Machiel80/esp32-serial-flasher/flashbox design/3d model/3d-model impression.png

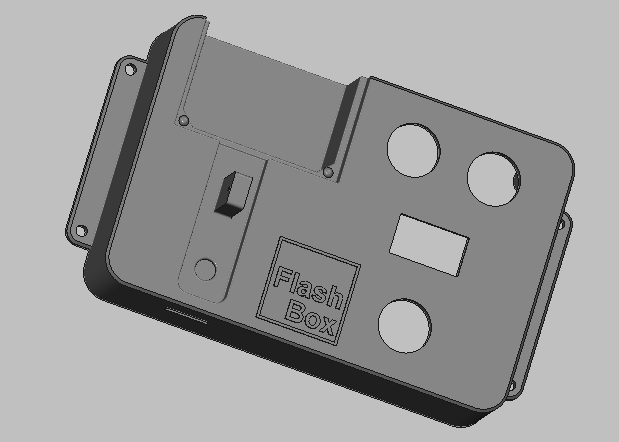
flashbox design/3d model/3d-model impression.png
