Machiel80/esp32-serial-flasher/flashbox design/3d model/20220907_FlashBox_left.png

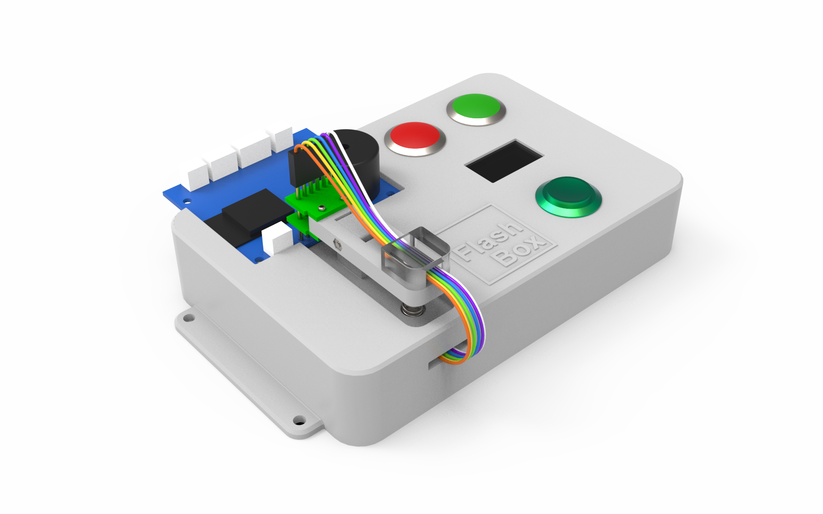
flashbox design/3d model/20220907_FlashBox_left.png
