Machiel80/esp32-serial-flasher/flashbox design/components/1 Usb cable/H7e599deed7ca4eed93aaca98d95c51f6y.jpg

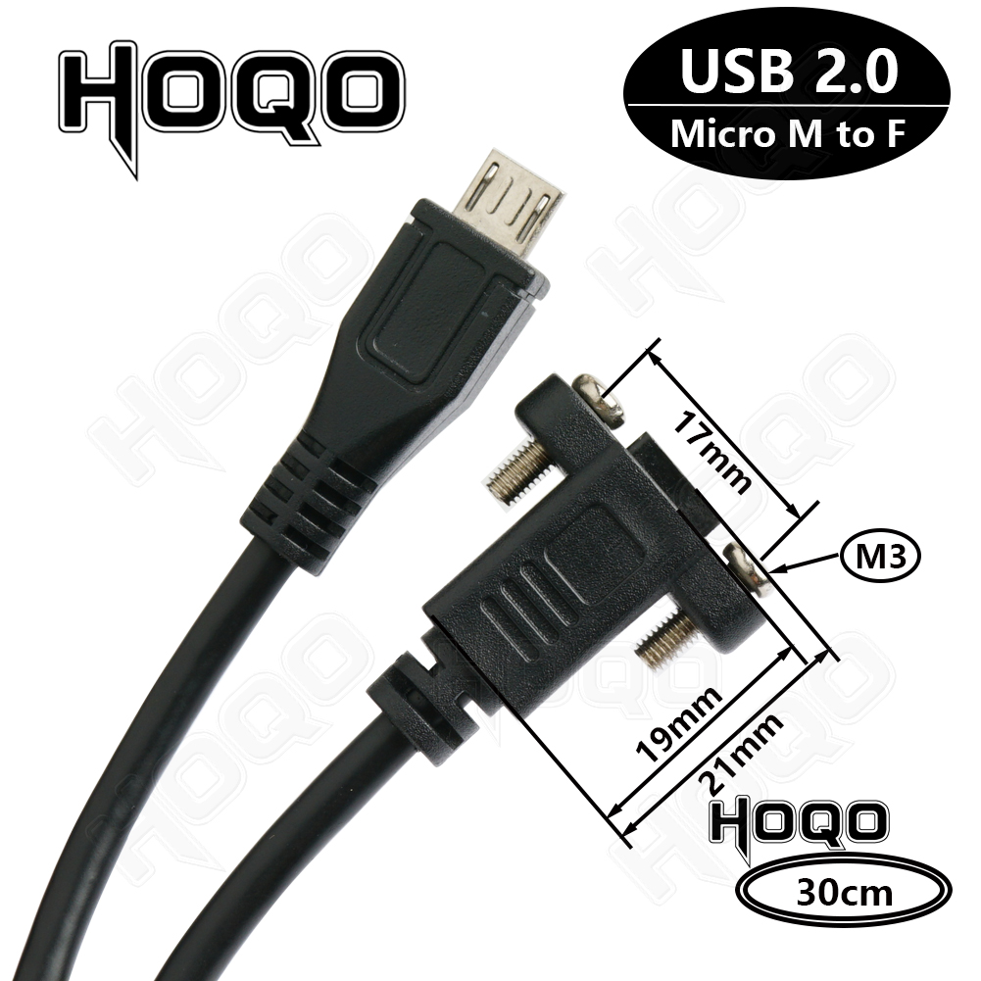
flashbox design/components/1 Usb cable/H7e599deed7ca4eed93aaca98d95c51f6y.jpg
