Machiel80/esp32-serial-flasher/flashbox design/components/1 Usb cable/H70d741a2f5fd48ce99fb8062a469d486L.jpg

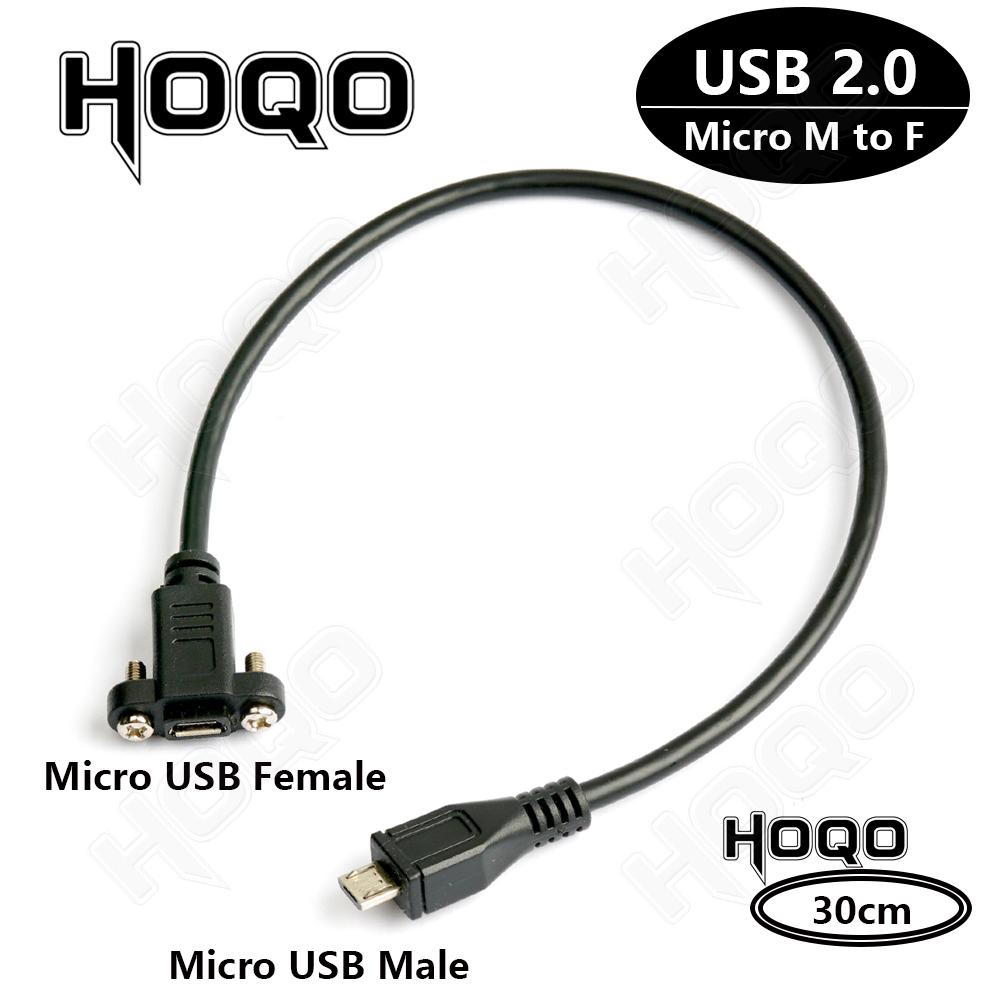
flashbox design/components/1 Usb cable/H70d741a2f5fd48ce99fb8062a469d486L.jpg
