Machiel80/esp32-serial-flasher/flashbox design/components/1 Usb cable/H580205805ddb444d95cb9cb375392fc0s.jpg

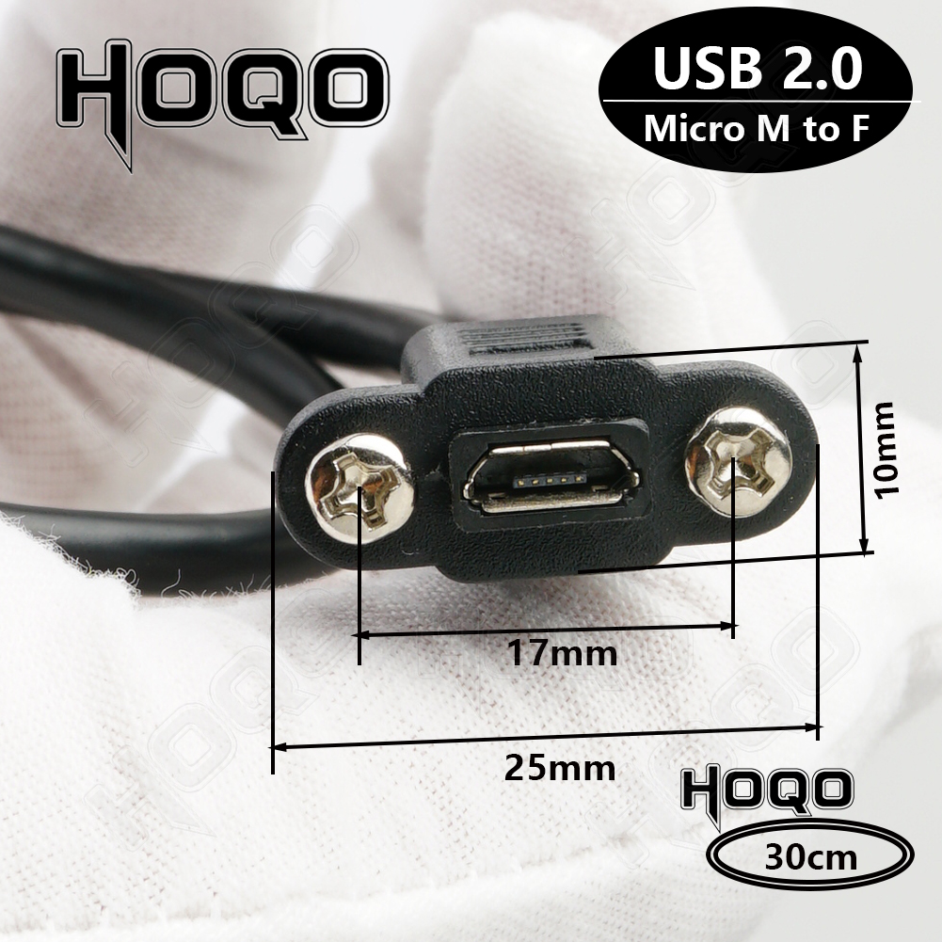
flashbox design/components/1 Usb cable/H580205805ddb444d95cb9cb375392fc0s.jpg
