Machiel80/esp32-serial-flasher/flashbox design/components/2 ESP32 devkit v1/72782579-1bceb700-3c4a-11ea-8157-d8394b984931.png

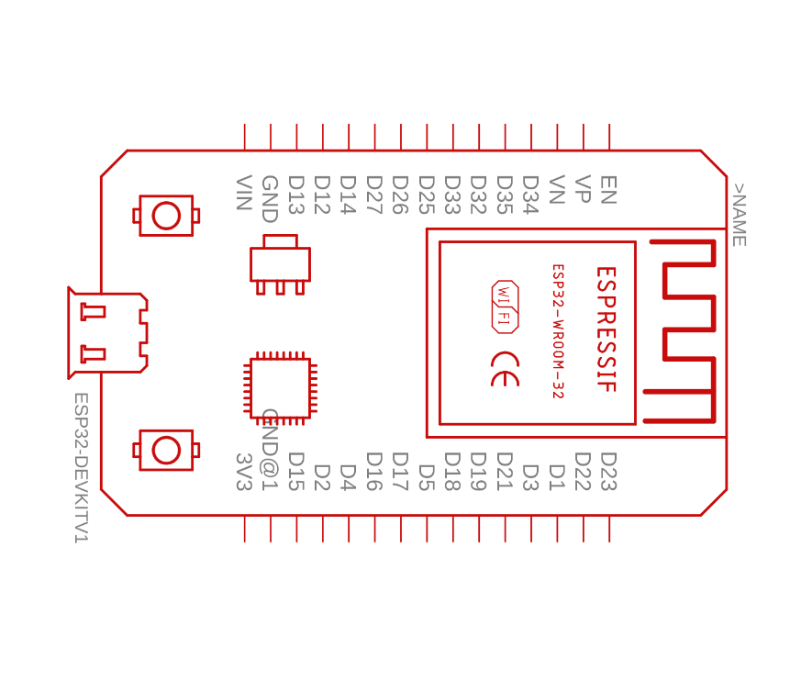
flashbox design/components/2 ESP32 devkit v1/72782579-1bceb700-3c4a-11ea-8157-d8394b984931.png
