Machiel80/esp32-serial-flasher/flashbox design/components/2 ESP32 devkit v1/72782582-1d987a80-3c4a-11ea-8e91-fc3043e2dca8.png

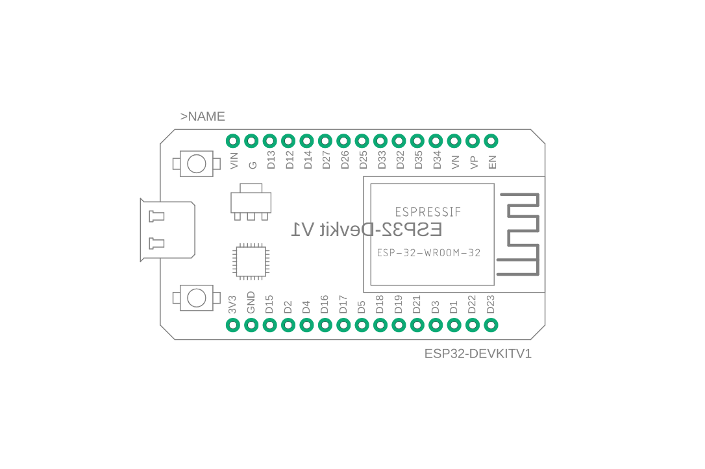
flashbox design/components/2 ESP32 devkit v1/72782582-1d987a80-3c4a-11ea-8e91-fc3043e2dca8.png
