Machiel80/esp32-serial-flasher/flashbox design/components/2 ESP32 devkit v1/edc50841300b4eb69d4db9c68fee543ab487c1be.webp

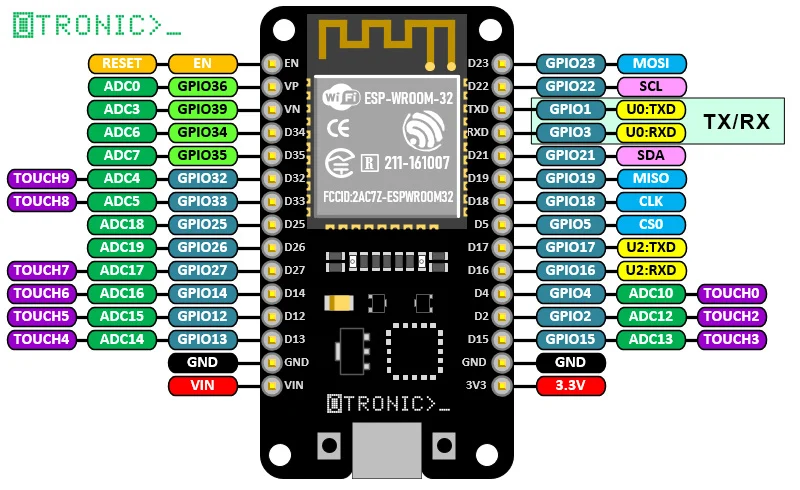
flashbox design/components/2 ESP32 devkit v1/edc50841300b4eb69d4db9c68fee543ab487c1be.webp
