Machiel80/esp32-serial-flasher/flashbox design/components/2 ESP32 devkit v1/HTB1lpVGicrI8KJjy0Fhq6zfnpXa4.webp

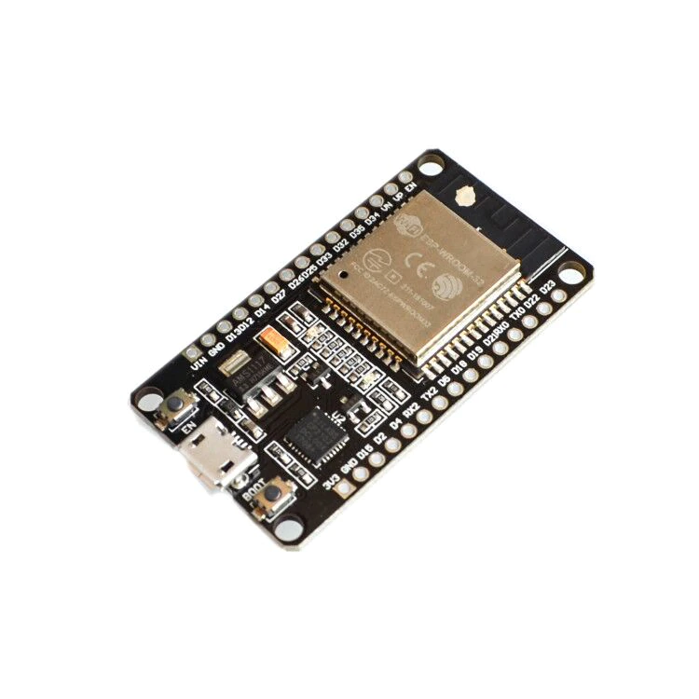
flashbox design/components/2 ESP32 devkit v1/HTB1lpVGicrI8KJjy0Fhq6zfnpXa4.webp
