Machiel80/esp32-serial-flasher/flashbox design/components/2 ESP32 devkit v1/HTB1yfV2if6H8KJjy0Fjq6yXepXax.webp

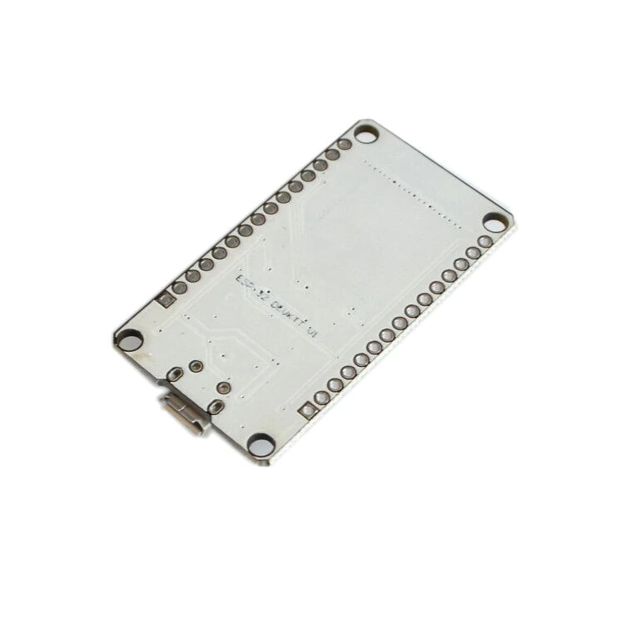
flashbox design/components/2 ESP32 devkit v1/HTB1yfV2if6H8KJjy0Fjq6yXepXax.webp
