Machiel80/esp32-serial-flasher/flashbox design/components/3 Six pin programmer module/41XIdj7KVcL.jpg

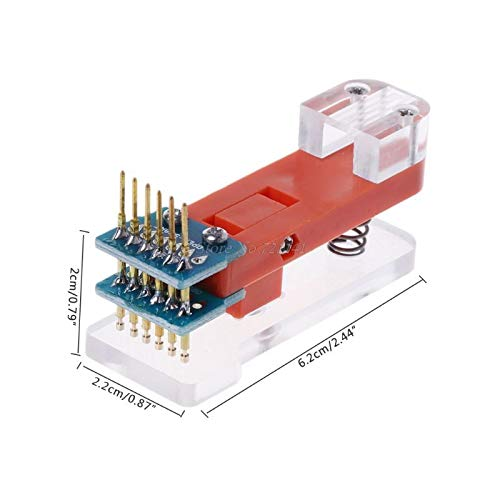
flashbox design/components/3 Six pin programmer module/41XIdj7KVcL.jpg
