Machiel80/esp32-serial-flasher/flashbox design/components/3 Six pin programmer module/esp32 6-connector b.png

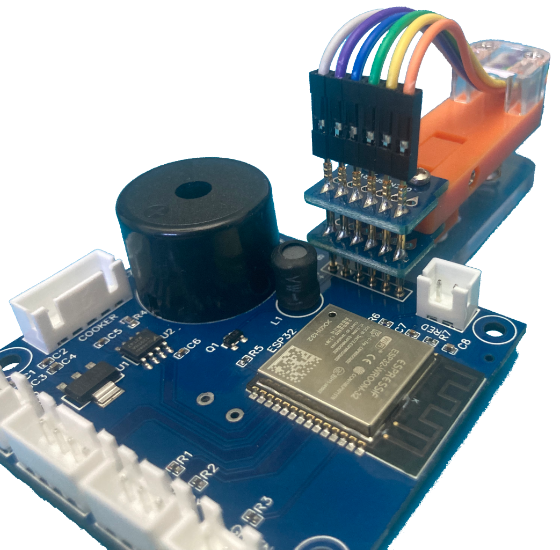
flashbox design/components/3 Six pin programmer module/esp32 6-connector b.png
