Machiel80/esp32-serial-flasher/flashbox design/components/3 Six pin programmer module/HTB1skHbacPEK1JjSZFEq6yA3XXaS.jpg

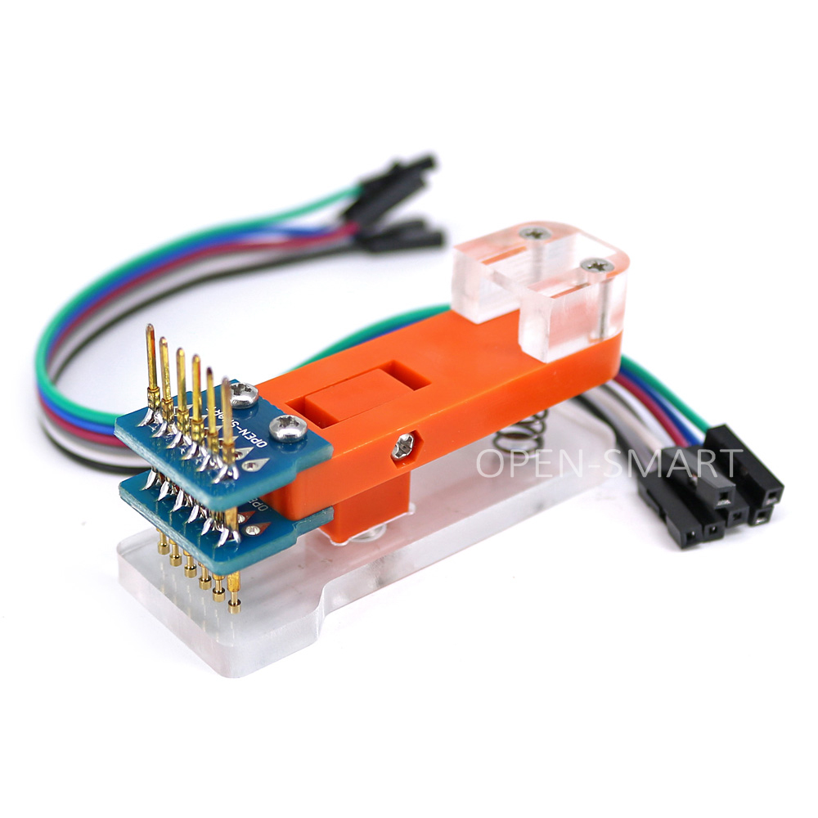
flashbox design/components/3 Six pin programmer module/HTB1skHbacPEK1JjSZFEq6yA3XXaS.jpg
