Machiel80/esp32-serial-flasher/flashbox design/components/4 Oled display SSD1306/H5f7c4044cbfd41a499ce24ac183757f1j.webp

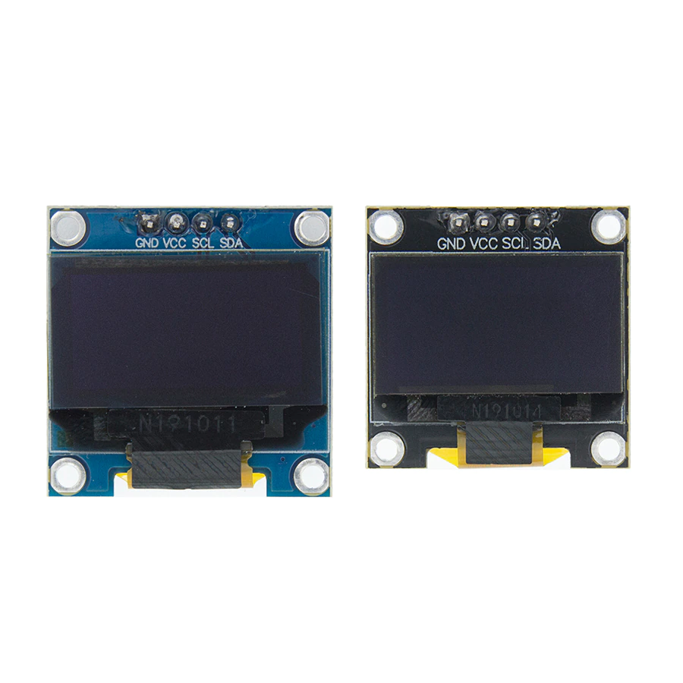
flashbox design/components/4 Oled display SSD1306/H5f7c4044cbfd41a499ce24ac183757f1j.webp
