Machiel80/esp32-serial-flasher/flashbox design/components/4 Oled display SSD1306/H711061da99bb47be8f3c3b8c4720aefbs.png

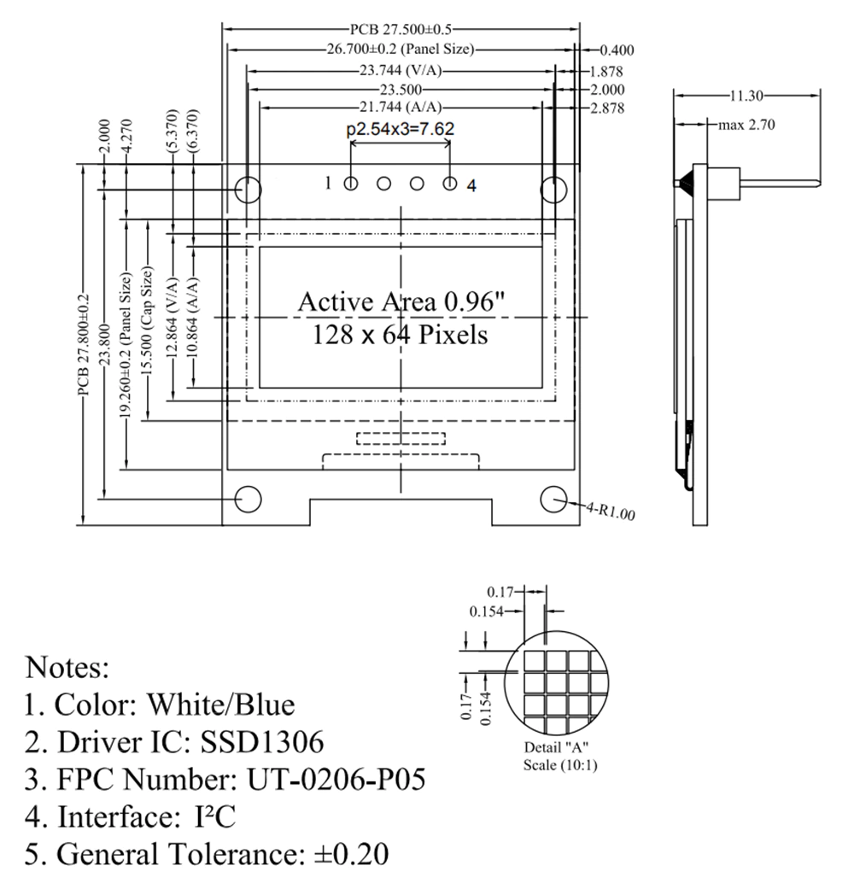
flashbox design/components/4 Oled display SSD1306/H711061da99bb47be8f3c3b8c4720aefbs.png
