Machiel80/esp32-serial-flasher/flashbox design/components/4 Oled display SSD1306/Ha7cd8adc92d04107a2148dfc41a41de7y.webp

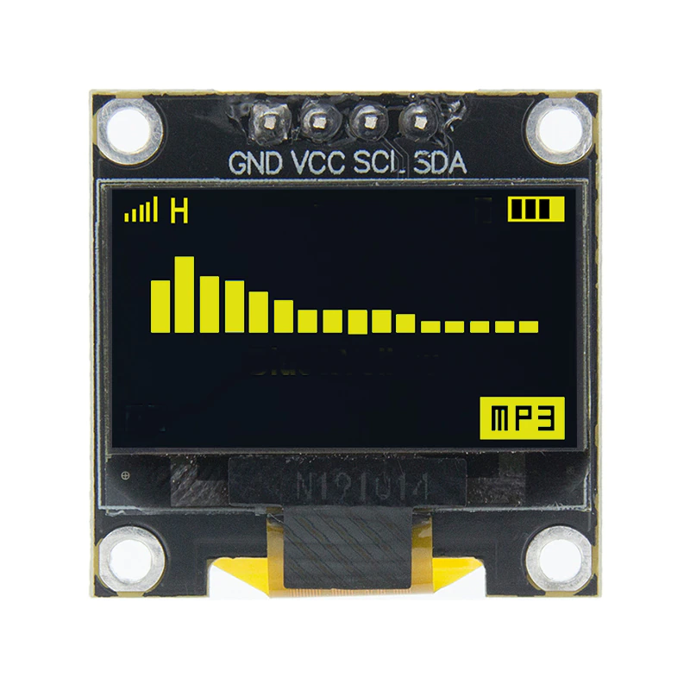
flashbox design/components/4 Oled display SSD1306/Ha7cd8adc92d04107a2148dfc41a41de7y.webp
