Machiel80/esp32-serial-flasher/flashbox design/components/4 Oled display SSD1306/Haface05d296b4e2284693b39635cb6cbS.webp

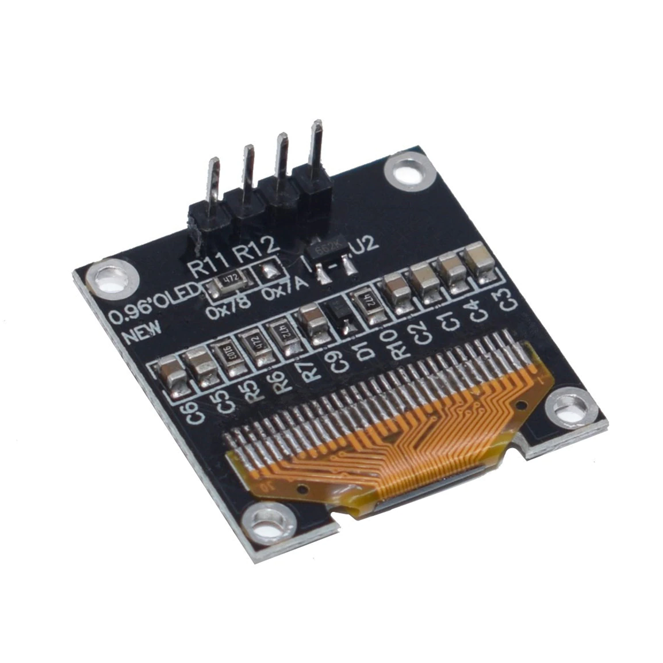
flashbox design/components/4 Oled display SSD1306/Haface05d296b4e2284693b39635cb6cbS.webp
