Machiel80/esp32-serial-flasher/flashbox design/components/4 Oled display SSD1306/He7448b22496b4b068e2d80eedcc6bdbaz.webp

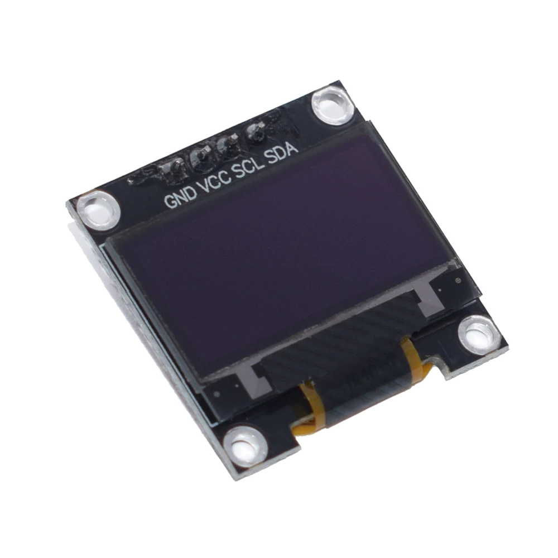
flashbox design/components/4 Oled display SSD1306/He7448b22496b4b068e2d80eedcc6bdbaz.webp
