Machiel80/esp32-serial-flasher/flashbox design/components/5-6 LED red and green 19mm 3-6 Volt/H4b428e8acbf04cc8bed7ae7006aec5bar.webp

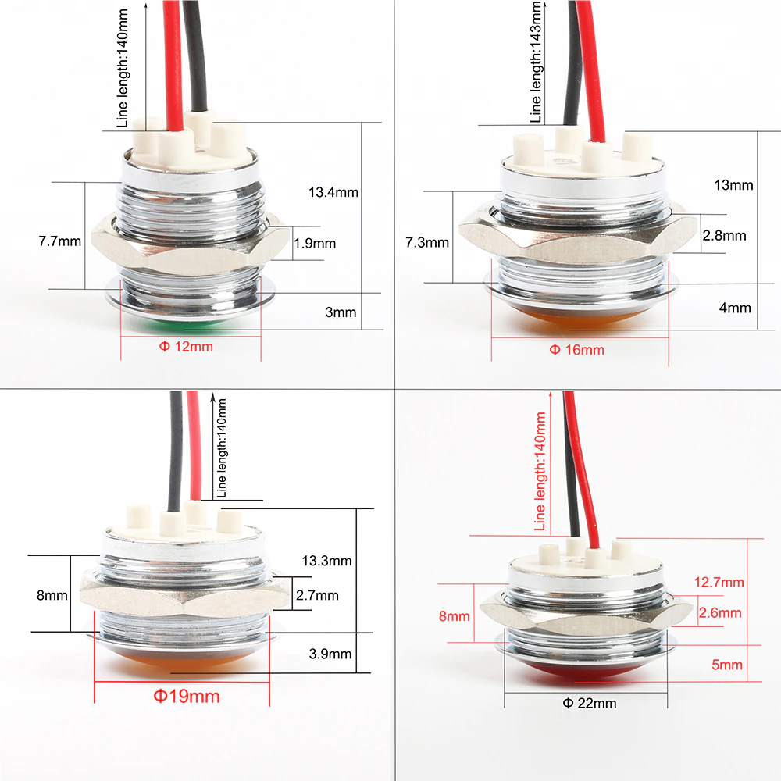
flashbox design/components/5-6 LED red and green 19mm 3-6 Volt/H4b428e8acbf04cc8bed7ae7006aec5bar.webp
