Machiel80/esp32-serial-flasher/flashbox design/components/5-6 LED red and green 19mm 3-6 Volt/H76da5ad4245a435994fc19493104bb181.webp

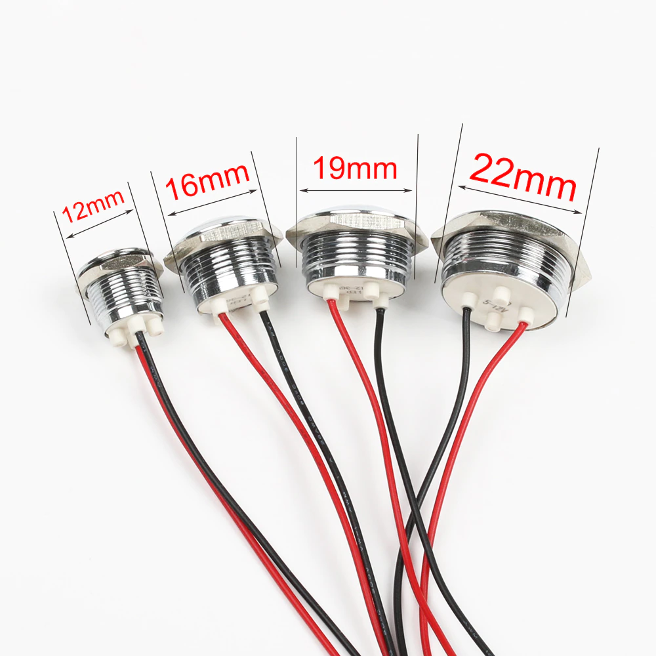
flashbox design/components/5-6 LED red and green 19mm 3-6 Volt/H76da5ad4245a435994fc19493104bb181.webp
