Machiel80/esp32-serial-flasher/flashbox design/components/5-6 LED red and green 19mm 3-6 Volt/H1882546c09fc4e979646f59378161bbeo.webp

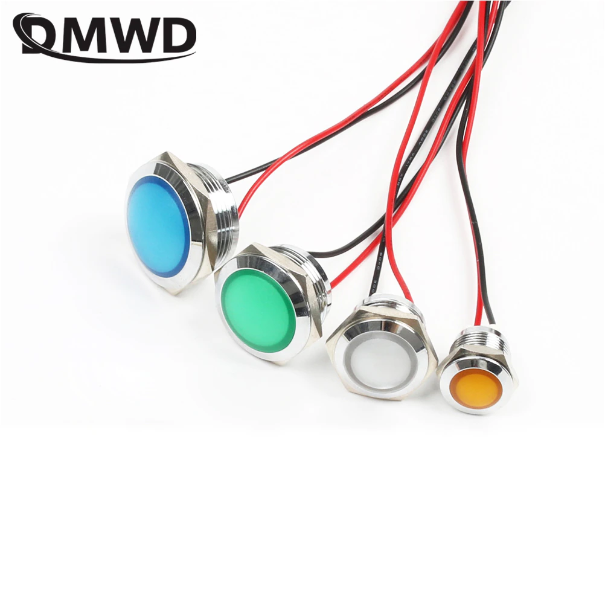
flashbox design/components/5-6 LED red and green 19mm 3-6 Volt/H1882546c09fc4e979646f59378161bbeo.webp
