Machiel80/esp32-serial-flasher/flashbox design/components/7 push button/H9f6b385dcf874d92bfd1f709ab0d7a955.webp

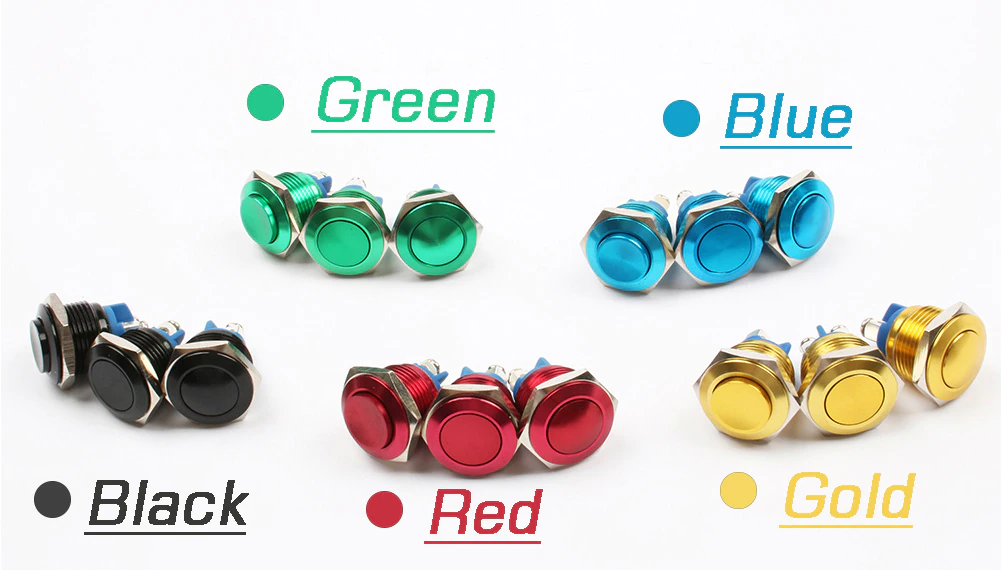
flashbox design/components/7 push button/H9f6b385dcf874d92bfd1f709ab0d7a955.webp
