Machiel80/esp32-serial-flasher/flashbox design/components/7 push button/H694e0852fec442c0ad46382c37578eeco.webp

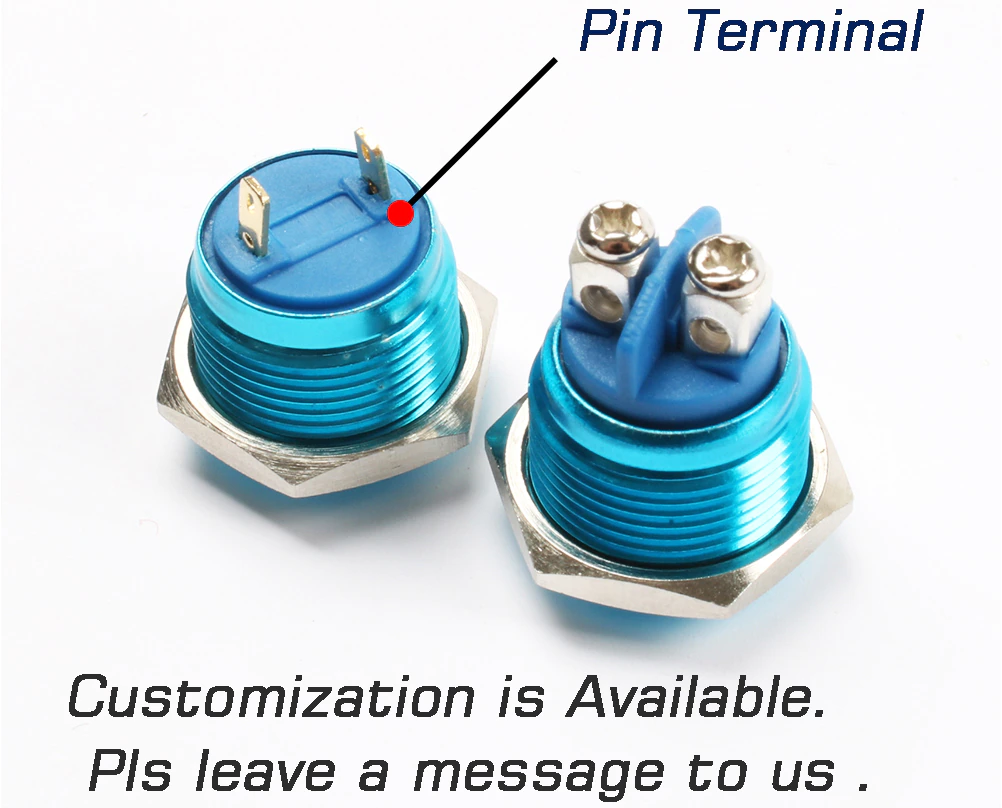
flashbox design/components/7 push button/H694e0852fec442c0ad46382c37578eeco.webp
