Machiel80/esp32-serial-flasher/flashbox design/components/7 push button/H6076d74d58c84e6cbe8248aaeefe02abr.webp

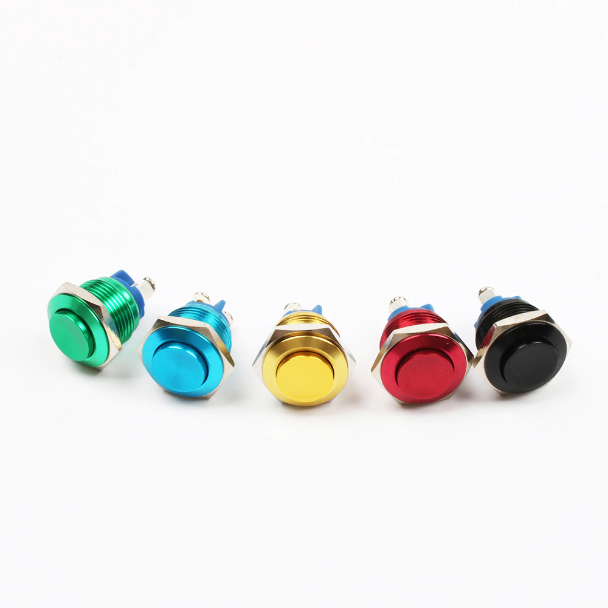
flashbox design/components/7 push button/H6076d74d58c84e6cbe8248aaeefe02abr.webp
