Machiel80/esp32-serial-flasher/flashbox design/components/7 push button/H7854d16cfe76469f831df59f06d8d8f33.webp

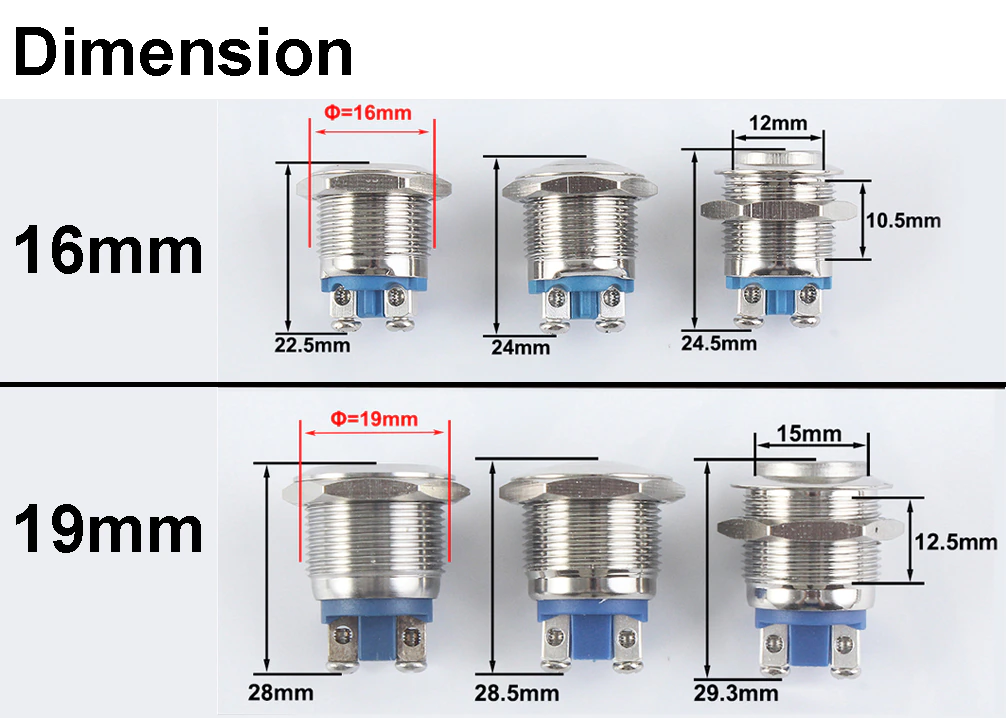
flashbox design/components/7 push button/H7854d16cfe76469f831df59f06d8d8f33.webp
