Machiel80/esp32-serial-flasher/flashbox design/components/7 push button/H63307287746d4fb285c3541f25835100M.webp

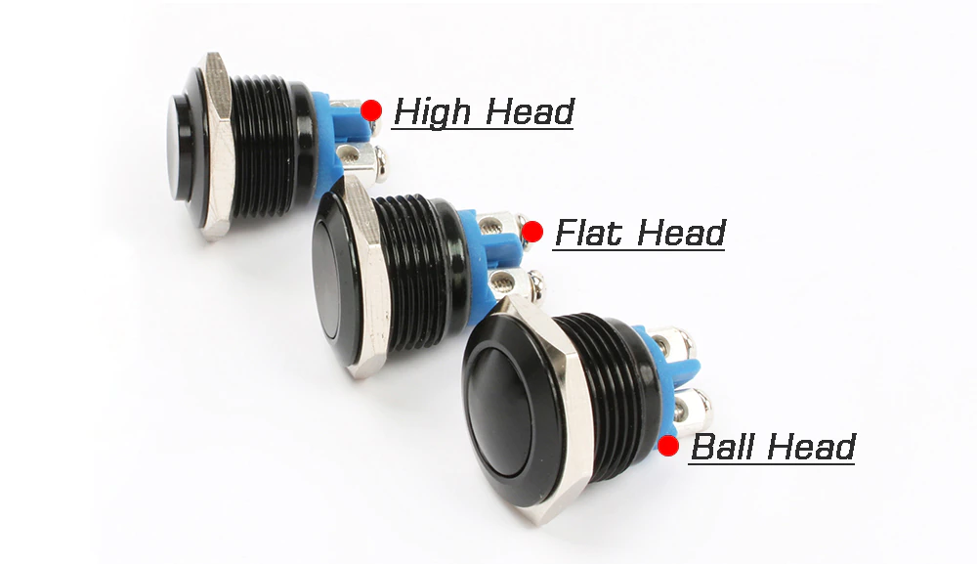
flashbox design/components/7 push button/H63307287746d4fb285c3541f25835100M.webp
