Machiel80/esp32-serial-flasher/flashbox design/components/7 push button/Ha0677f4018a84cb58004bcae4c201d344.webp

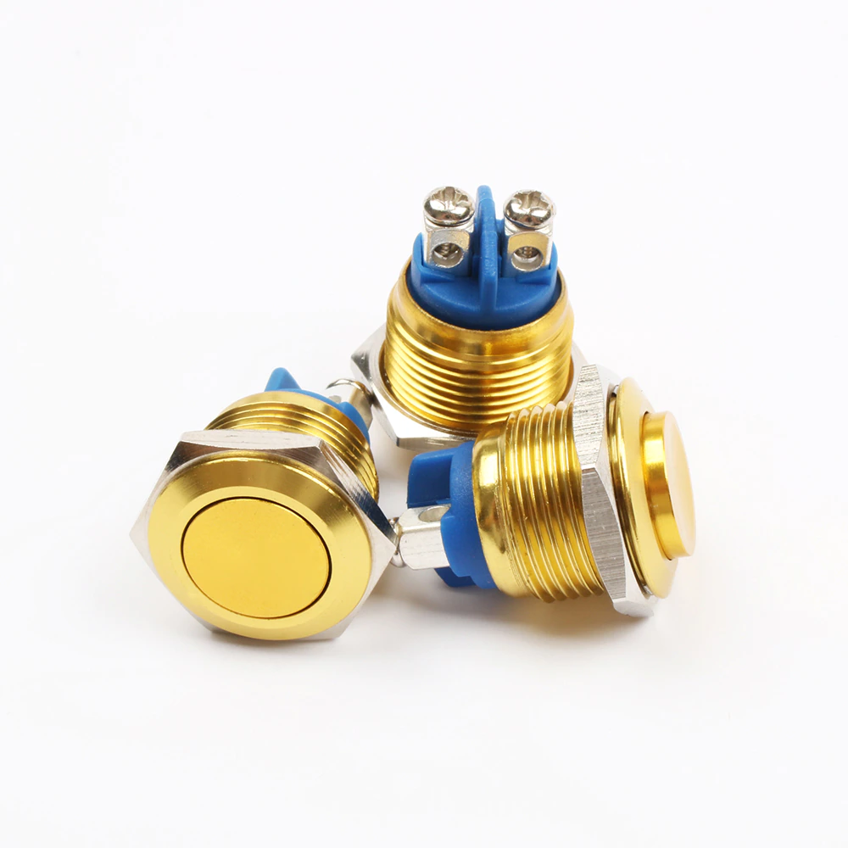
flashbox design/components/7 push button/Ha0677f4018a84cb58004bcae4c201d344.webp
