Machiel80/esp32-serial-flasher/flashbox design/components/3 Six pin programmer module/HTB1QprNXMvGK1Jjy0Faq6z7lpXan.jpg

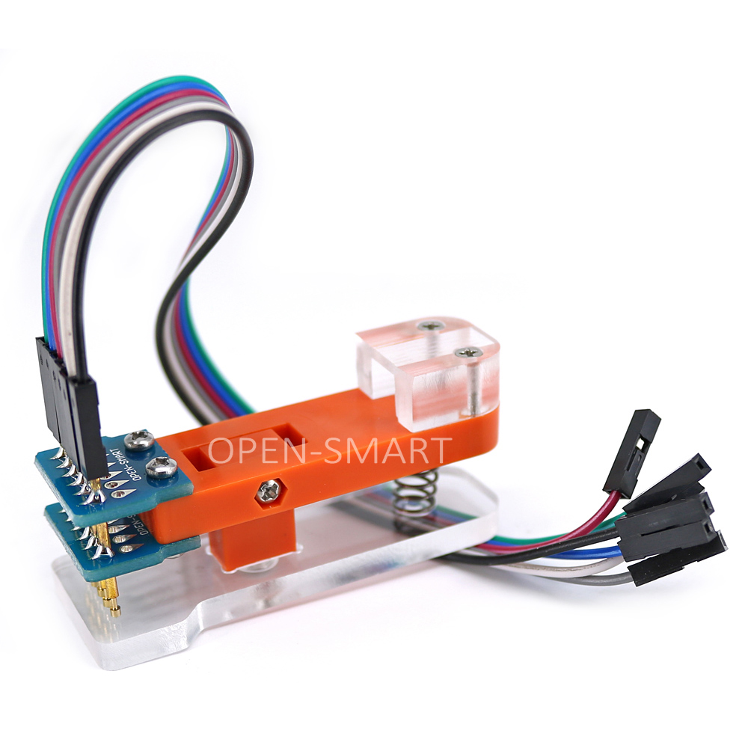
flashbox design/components/3 Six pin programmer module/HTB1QprNXMvGK1Jjy0Faq6z7lpXan.jpg
