Machiel80/esp32-serial-flasher/main/icons.h

// used: https://convertio.co/bmp-xbm/
//
// icon_completed
// icon_failed
// icon_progress_1_3
// icon_progress_2_3
// icon_progress_3_3
// icon_open


// 'icon_completed', 64x64px
const uint8_t icon_completed [] = {
  0x00, 0x00, 0x00, 0xB8, 0x0F, 0x00, 0x00, 0x00, 0x00, 0x00, 0x80, 0xFF, 
  0xFF, 0x01, 0x00, 0x00, 0x00, 0x00, 0xF0, 0xFF, 0xFF, 0x0F, 0x00, 0x00, 
  0x00, 0x00, 0xFC, 0xFF, 0xFF, 0x3F, 0x00, 0x00, 0x00, 0x00, 0xFF, 0x7F, 
  0xFE, 0xFF, 0x00, 0x00, 0x00, 0x80, 0xFF, 0x01, 0x80, 0xFF, 0x03, 0x00, 
  0x00, 0xE0, 0x3F, 0x00, 0x00, 0xF8, 0x07, 0x00, 0x00, 0xF0, 0x0F, 0x00, 
  0x00, 0xF0, 0x1F, 0x00, 0x00, 0xF8, 0x03, 0x00, 0x00, 0xC0, 0x1F, 0x00, 
  0x00, 0xFC, 0x00, 0x00, 0x00, 0x00, 0x7F, 0x00, 0x00, 0x7E, 0x00, 0x00, 
  0x00, 0x00, 0xFE, 0x00, 0x00, 0x3F, 0x00, 0x00, 0x00, 0x00, 0xFC, 0x00, 
  0x80, 0x1F, 0x00, 0x00, 0x00, 0x00, 0xF8, 0x01, 0xC0, 0x0F, 0x00, 0x00, 
  0x00, 0x00, 0xF0, 0x03, 0xC0, 0x07, 0x00, 0x00, 0x00, 0x00, 0xE0, 0x07, 
  0xE0, 0x03, 0x00, 0x00, 0x00, 0x00, 0xC0, 0x07, 0xF0, 0x03, 0x00, 0x00, 
  0x00, 0x00, 0x80, 0x0F, 0xF0, 0x01, 0x00, 0x00, 0x00, 0x00, 0x80, 0x0F, 
  0xF8, 0x00, 0x00, 0x00, 0x00, 0x00, 0x00, 0x1F, 0xF8, 0x00, 0x00, 0x00, 
  0x00, 0x00, 0x00, 0x3E, 0x7C, 0x00, 0x00, 0x00, 0x00, 0x60, 0x00, 0x3E, 
  0x7C, 0x00, 0x00, 0x00, 0x00, 0xF0, 0x00, 0x3E, 0x3C, 0x00, 0x00, 0x00, 
  0x00, 0xF8, 0x01, 0x7C, 0x3E, 0x00, 0x00, 0x00, 0x00, 0xFC, 0x03, 0x7C, 
  0x3E, 0x00, 0x00, 0x00, 0x00, 0xFE, 0x03, 0x78, 0x3E, 0x00, 0x00, 0x00, 
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
  0x3E, 0x00, 0x00, 0x00, 0x00, 0x00, 0x00, 0x7C, 0x3E, 0x00, 0x00, 0x00, 
  0x00, 0x00, 0x00, 0x7C, 0x3C, 0x00, 0x00, 0x00, 0x00, 0x00, 0x00, 0x3C, 
  0x7C, 0x00, 0x00, 0x00, 0x00, 0x00, 0x00, 0x3E, 0x7C, 0x00, 0x00, 0x00, 
  0x00, 0x00, 0x00, 0x3E, 0xF8, 0x00, 0x00, 0x00, 0x00, 0x00, 0x00, 0x1F, 
  0xF8, 0x00, 0x00, 0x00, 0x00, 0x00, 0x00, 0x1F, 0xF0, 0x01, 0x00, 0x00, 
  0x00, 0x00, 0x80, 0x0F, 0xF0, 0x01, 0x00, 0x00, 0x00, 0x00, 0x80, 0x0F, 
  0xE0, 0x03, 0x00, 0x00, 0x00, 0x00, 0xC0, 0x07, 0xE0, 0x07, 0x00, 0x00, 
  0x00, 0x00, 0xE0, 0x07, 0xC0, 0x0F, 0x00, 0x00, 0x00, 0x00, 0xF0, 0x03, 
  0x80, 0x1F, 0x00, 0x00, 0x00, 0x00, 0xF8, 0x01, 0x00, 0x3F, 0x00, 0x00, 
  0x00, 0x00, 0xFC, 0x00, 0x00, 0x7F, 0x00, 0x00, 0x00, 0x00, 0x7E, 0x00, 
  0x00, 0xFC, 0x00, 0x00, 0x00, 0x00, 0x7F, 0x00, 0x00, 0xFC, 0x03, 0x00, 
  0x00, 0xC0, 0x1F, 0x00, 0x00, 0xF8, 0x0F, 0x00, 0x00, 0xF0, 0x0F, 0x00, 
  0x00, 0xE0, 0x3F, 0x00, 0x00, 0xFC, 0x07, 0x00, 0x00, 0xC0, 0xFF, 0x01, 
  0x80, 0xFF, 0x03, 0x00, 0x00, 0x00, 0xFF, 0xBF, 0xFD, 0xFF, 0x00, 0x00, 
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
};
